andionea/steerturnillum/4_Engineering/1_Software/2_Development/1_Sources/4_EcuAbstraction/Btn/Design/SwDe_Btn.docx

Btn Software Design

SteerTurnIllum


Author: | | Nicolae-Bogdan Bacrău
Version: | | 1.0

# Index

# 1 Glossary

This section contains a glossary of all the important terms and acronyms used inside the document.

Term / Acronym | Description
AUTOSAR | AUTomotive Open System ARchitecture
VFB | Virtual Functional Bus
SWC | Software Component
RTE | Runtime Environment
BSW | Basic Software
OS | Operating System
S/R | Sender / Receiver
C/S | Client / Server
ECU | Electronic Control Unit
uC | Microcontroller
ADC | Analog Digital Converter
DIO | Digital Input / Output
PWM | Pulse Width Modulation

Table 1 - Glossary.

# 2 Introduction

## Purpose of the Document

The purpose of the document is to define the software design of the Btn SWC for the SteerTurnIllum embedded academy project.

## Overview

The Btn SWC implements the reading, debouncing and active values processing of all the button inputs, proving a simple button pressed or not pressed status.

# 3 Design Requirements

[SWDE_BTN_1] The Btn SWC shall adhere to the structure illustrated in the composite structure diagram from Figure 1.

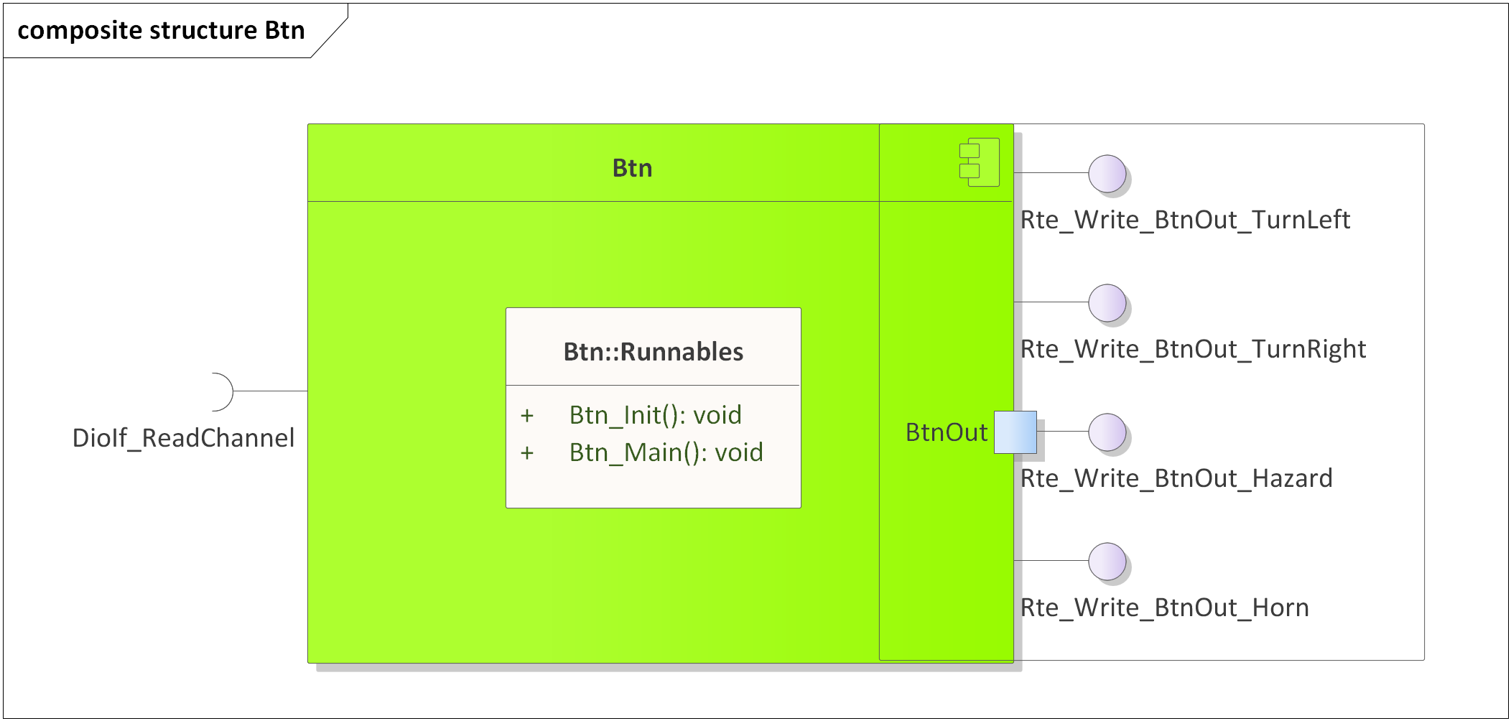
[picture p30: figure]

Figure 1 - Btn composite structure diagram.

[SWDE_BTN_2] The Btn SWC shall assure a debouncing mechanism according to Chapter 3.2 and [SYRE_GEN_11] from the System Requirements.
[SWDE_BTN_3] The Btn SWC shall adhere to the SWC file structure template from 4_Engineering\1_Software\2_Development\1_Sources\8_Templates\Swc\Code.
[SWDE_BTN_4] The Btn SWC shall contain the following configuration parameters:
- In Btn_Cfg.h:
  - BTN_MAIN_PERIODICITY_US: macro defining the periodicity of the main function in microseconds.
  - BTN_DEBOUNCE_WINDOW_US: macro defining the debounce window for all the buttons, in microseconds.
  - BTN_NUMBER_OF_INSTANCES: macro defining the number of button instances to be processed in the main function.
  - BTN_*_INSTANCE: zero based macros defining unique IDs of all the button instances, needed for the interaction between the core and RTE.
- In Btn_Cfg.c:
  - Btn_gkat_Config[BTN_NUMBER_OF_INSTANCES]: internal global constant array defining the active value (STD_HIGH or STD_LOW) and the DioIf channel for all the button channels.
[SWDE_BTN_5] The Btn SWC shall implement the void Btn_Init(void) runnable for initializing all the internal static and global variables.
[SWDE_BTN_6] The Btn SWC shall implement the void Btn_Main(void) runnable for implementing the processing of all the button instances as follows:
  - Reads the button DIO channels through DioIf_ReadChannel().
  - Calculates the current raw press state depending on the configured active press state in comparison with the actual read DIO level.
  - Applies the debounce algorithm on the current raw press state.
  - Writes the debounced buttons status to the RTE through Rte_Write_BtnOut_*(). RTE_BTN_INIT status shall be reported until a full (successful) debounce has been performed since the initialization.
[SWDE_BTN_7] The Btn SWC shall include DioIf.h and directly use the DioIf_ReadChannel() function for reading the button DioIf channels.

# 4 Information about this Document

## 1.1 Copyright

All rights, including translation rights, are reserved. Under no circumstances shall any fragment of this document be reproduced without written authorization from NTT DATA Romania S.A, including copying, photographing or replicating through other methods.

Copyright (c) NTT DATA Romania S.A.

## 1.2 Version Index

Version | Date | Author | Chapter | Modification description
1.0 | 10.07.2021 | Nicolae-Bogdan Bacrău | All | Created.

Table 2 - Version Index.

Copyright © NTT DATA Romania S.A. Page 6 of 7

Information Type: Working Standard Information Owner: Nicolae-Bogdan Bacrău Company: NTT DATA Romania
