andionea/steerturnillum/4_Engineering/1_Software/2_Development/1_Sources/5_Mcal/Dio/Design/SwDe_Dio.docx

Dio Software Design

SteerTurnIllum


Author: | | Nicolae-Bogdan Bacrău
Version: | | 1.0

# Index

# 1 Glossary

This section contains a glossary of all the important terms and acronyms used inside the document.

Term / Acronym | Description
AUTOSAR | AUTomotive Open System ARchitecture
VFB | Virtual Functional Bus
SWC | Software Component
RTE | Runtime Environment
BSW | Basic Software
OS | Operating System
S/R | Sender / Receiver
C/S | Client / Server
ECU | Electronic Control Unit
uC | Microcontroller
ADC | Analog Digital Converter
DIO | Digital Input / Output
PWM | Pulse Width Modulation

Table 1 - Glossary.

# 2 Introduction

## Purpose of the Document

The purpose of the document is to define the software design of the Dio driver for the SteerTurnIllum embedded academy project.

## Overview

While the AUTOSAR Dio module is complex and is usually configured via generators, in this project it is manually implemented and its features are limited to:

- Reading and writing channels.
- Reading and writing ports.

# 3 Design Requirements

[SWDE_DIO_1] The Dio driver shall be implemented according to AUTOSAR 4.3.1 specifications.
[SWDE_DIO_2] The Dio driver shall implement the following interfaces and all their required data types for reading and writing DIO channels and ports:
- Dio_ReadChannel();
- Dio_WriteChannel();
- Dio_FlipChannel();
- Dio_ReadPort();
- Dio_WritePort();
[SWDE_DIO_3] The Dio driver shall consist of the following files:
- Dio.c: Implements all the required interfaces in a generic way.
- Dio.h: Exports all the required interfaces, data types and the link-time configuration.
- Dio_Lcfg.c: Defines the list of registers and masks to be used for reading and writing DIO channels and ports.
- Dio_Cfg.h: Defines and exports the following:
  - DIO_API_CHANNELS macro: defining if the DIO channels APIs are activated or not (STD_ON or STD_OFF).
  - DIO_API_PORTS macro: defining if the DIO ports APIs are activated or not (STD_ON or STD_OFF).
  - DIO_NUMBER_OF_PORTS macro: number of configured DIO ports.
  - DIO_<Port_ID> macros: zero based IDs of all the DIO ports.
  - DIO_NUMBER_OF_CHANNELS macro: number of configured DIO channels.
  - DIO_<Port_ID>_<Port_Pin_ID> macros: zero based IDs of all the DIO channels.

# 4 Information about this Document

## 1.1 Copyright

All rights, including translation rights, are reserved. Under no circumstances shall any fragment of this document be reproduced without written authorization from NTT DATA Romania S.A, including copying, photographing or replicating through other methods.

Copyright (c) NTT DATA Romania S.A.

## 1.2 Version Index

Version | Date | Author | Chapter | Modification description
1.0 | 10.07.2021 | Nicolae-Bogdan Bacrău | All | Created.

Table 2 - Version Index.

Copyright © NTT DATA Romania S.A. Page 6 of 7

Information Type: Working Standard Information Owner: Nicolae-Bogdan Bacrău Company: NTT DATA Romania
