andionea/steerturnillum/4_Engineering/1_Software/2_Development/1_Sources/5_Mcal/Pwm/Design/SwDe_Pwm.docx

Pwm Software Design

SteerTurnIllum


Author: | | Nicolae-Bogdan Bacrău
Version: | | 1.0

# Index

# 1 Glossary

This section contains a glossary of all the important terms and acronyms used inside the document.

Term / Acronym | Description
AUTOSAR | AUTomotive Open System ARchitecture
VFB | Virtual Functional Bus
SWC | Software Component
RTE | Runtime Environment
BSW | Basic Software
OS | Operating System
S/R | Sender / Receiver
C/S | Client / Server
ECU | Electronic Control Unit
uC | Microcontroller
ADC | Analog Digital Converter
DIO | Digital Input / Output
PWM | Pulse Width Modulation

Table 1 - Glossary.

# 2 Introduction

## Purpose of the Document

The purpose of the document is to define the software design of the Pwm driver for the SteerTurnIllum embedded academy project.

## Overview

While the AUTOSAR Pwm module is complex and is usually configured via generators, in this project it is manually implemented and its features are limited to:

- Configuring PWM channels.
- Writing PWM duty cycles.

# 3 Design Requirements

[SWDE_PWM_1] The Pwm driver shall be implemented according to AUTOSAR 4.3.1 specifications.
[SWDE_PWM_2] The Pwm driver shall implement the following interfaces and all their required data types for configuring PWM channels (timer configurations) and writing PWM duty cycles:
- Pwm_Init();
- Pwm_SetDutyCycle();
[SWDE_PWM_3] The Pwm driver shall include Init.h and directly use the Init_gv_Full*Bits() and / or Init_gv_Masked*Bits() functions for loading registers.
[SWDE_PWM_4] The Pwm driver shall consist of the following files:
- Pwm.c: Implements all the required interfaces in a generic way.
- Pwm.h: Exports all the required interfaces, data types and the post-build configuration.
- Pwm_PBcfg.c: Defines the list of registers and values to be written for setting the timers in PWM mode, setting the periods of the PWM channels and the PWM initial duty cycles.
- Pwm_Cfg.h: Defines and exports the following:
  - PWM_API_SET_DUTY_CYCLE macro: defining if the PWM API for setting duty cycles is activated or not (STD_ON or STD_OFF).
  - PWM_NUMBER_OF_CHANNELS macro: number of configured PWM channels.
  - PWM_<Port_ID>_<Port_Pin_ID> macros: zero based IDs of all the PWM channels.

# 4 Information about this Document

## 1.1 Copyright

All rights, including translation rights, are reserved. Under no circumstances shall any fragment of this document be reproduced without written authorization from NTT DATA Romania S.A, including copying, photographing or replicating through other methods.

Copyright (c) NTT DATA Romania S.A.

## 1.2 Version Index

Version | Date | Author | Chapter | Modification description
1.0 | 10.07.2021 | Nicolae-Bogdan Bacrău | All | Created.

Table 2 - Version Index.

Copyright © NTT DATA Romania S.A. Page 6 of 7

Information Type: Working Standard Information Owner: Nicolae-Bogdan Bacrău Company: NTT DATA Romania
