andionea/steerturnillum/4_Engineering/1_Software/2_Development/1_Sources/4_EcuAbstraction/Buzz/Design/SwDe_Buzz.docx

Buzz Software Design

SteerTurnIllum


Author: | | Nicolae-Bogdan Bacrău
Version: | | 1.0

# Index

# 1 Glossary

This section contains a glossary of all the important terms and acronyms used inside the document.

Term / Acronym | Description
AUTOSAR | AUTomotive Open System ARchitecture
VFB | Virtual Functional Bus
SWC | Software Component
RTE | Runtime Environment
BSW | Basic Software
OS | Operating System
S/R | Sender / Receiver
C/S | Client / Server
ECU | Electronic Control Unit
uC | Microcontroller
ADC | Analog Digital Converter
DIO | Digital Input / Output
PWM | Pulse Width Modulation

Table 1 - Glossary.

# 2 Introduction

## Purpose of the Document

The purpose of the document is to define the software design of the Buzz SWC for the SteerTurnIllum embedded academy project.

## Overview

The Buzz SWC implements a simple mute or buzzing control of buzzers.

# 3 Design Requirements

[SWDE_BUZZ_1] The Buzz SWC shall adhere to the structure illustrated in the composite structure diagram from Figure 1.

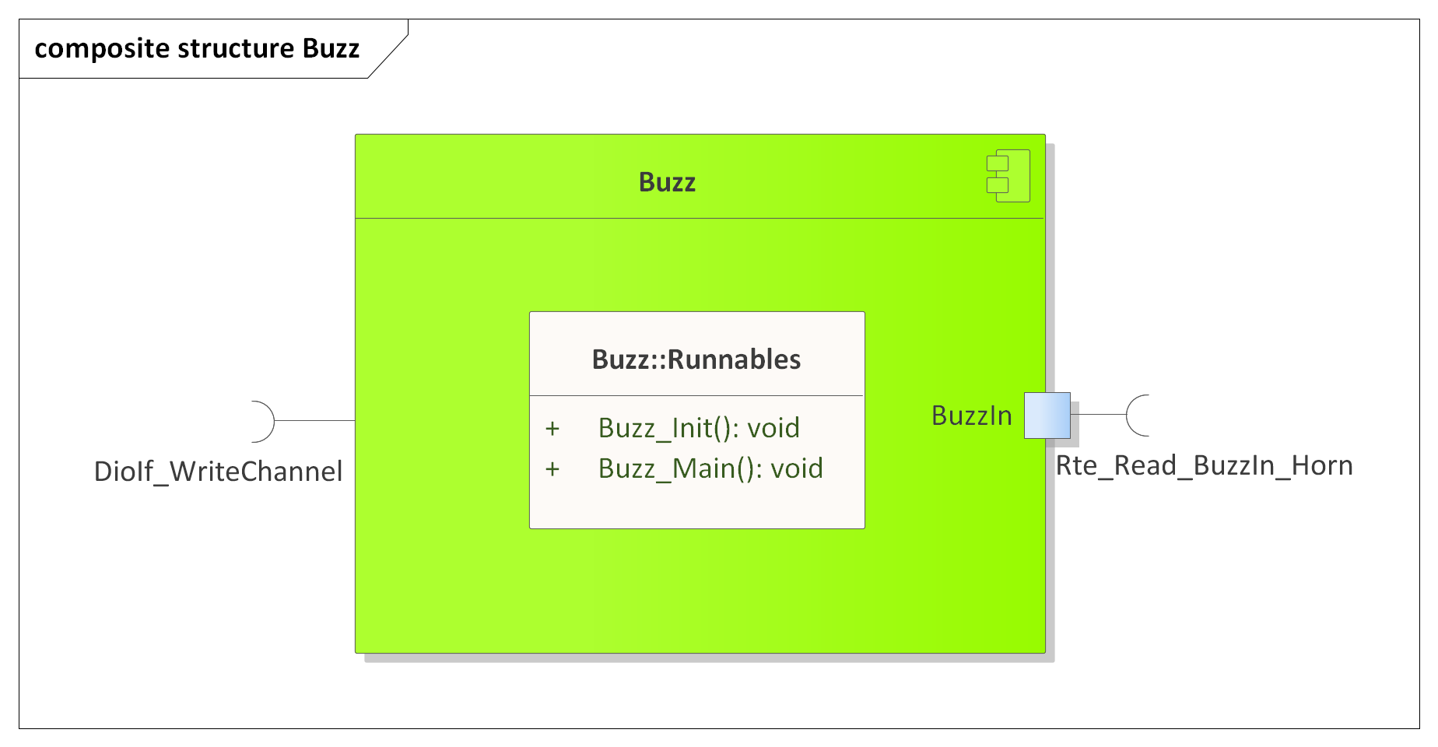
[picture p34: figure]

Figure 1 - Buzz composite structure diagram.

[SWDE_BUZZ_2] The Buzz SWC shall adhere to the SWC file structure template from 4_Engineering\1_Software\2_Development\1_Sources\8_Templates\Swc\Code.
[SWDE_BUZZ_3] The Buzz SWC shall contain the following configuration parameters:
- In Buzz_Cfg.h:
  - BUZZ_NUMBER_OF_INSTANCES: macro defining the number of buzzer instances to be processed in the main function.
  - BUZZ_*_INSTANCE: zero based macros defining unique IDs of all the buzzer instances, needed for the interaction between the core and RTE.
- In Buzz_Cfg.c:
  - Buzz_gkat_Config[BUZZ_NUMBER_OF_INSTANCES]: internal global constant array defining the VCC and IO DioIf channels for all buzzer instances.
[SWDE_BUZZ_4] The Buzz SWC shall implement the void Buzz_Init(void) runnable for initializing all the internal static and global variables and setting the buzzer in the mute state through DioIf_WriteChannel().
[SWDE_BUZZ_5] The Buzz SWC shall implement the void Buzz_Main(void) runnable for implementing the processing of all the buzzer instances as follows:
  - Reads the buzzer input control data through Rte_Read_BuzzIn_*().
  - Sets the buzzer state according to the read input control data: mute if RTE_BUZZ_OFF, buzzing if RTE_BUZZ_ON, through DioIf_WriteChannel(). Any other input control value shall be ignored.
[SWDE_BUZZ_6] The Buzz SWC shall include DioIf.h and directly use the DioIf_WriteChannel() function for writing the buzzer DioIf channels.

# 4 Information about this Document

## 1.1 Copyright

All rights, including translation rights, are reserved. Under no circumstances shall any fragment of this document be reproduced without written authorization from NTT DATA Romania S.A, including copying, photographing or replicating through other methods.

Copyright (c) NTT DATA Romania S.A.

## 1.2 Version Index

Version | Date | Author | Chapter | Modification description
1.0 | 10.07.2021 | Nicolae-Bogdan Bacrău | All | Created.

Table 2 - Version Index.

Copyright © NTT DATA Romania S.A. Page 6 of 7

Information Type: Working Standard Information Owner: Nicolae-Bogdan Bacrău Company: NTT DATA Romania
