andionea/steerturnillum/4_Engineering/1_Software/2_Development/1_Sources/7_Libraries/Efx/Design/SwDe_Efx.docx

Efx Software Design

SteerTurnIllum


Author: | | Nicolae-Bogdan Bacrău
Version: | | 1.0

# Index

# 1 Glossary

This section contains a glossary of all the important terms and acronyms used inside the document.

Term / Acronym | Description
AUTOSAR | AUTomotive Open System ARchitecture
VFB | Virtual Functional Bus
SWC | Software Component
RTE | Runtime Environment
BSW | Basic Software
OS | Operating System
S/R | Sender / Receiver
C/S | Client / Server
ECU | Electronic Control Unit
uC | Microcontroller
ADC | Analog Digital Converter
DIO | Digital Input / Output
PWM | Pulse Width Modulation

Table 1 - Glossary.

# 2 Introduction

## Purpose of the Document

The purpose of the document is to define the software design of the Efx library for the SteerTurnIllum embedded academy project.

## Overview

While the AUTOSAR Efx library contains more methods, in this project it implements a single interface for performing moving averages on uint16 inputs and outputs.

# 3 Design Requirements

[SWDE_EFX_1] The Efx library shall be implemented according to AUTOSAR 4.3.1 specifications.
[SWDE_EFX_2] The Efx library shall implement the following interfaces and all their required data types for performing moving averages on uint16 inputs and outputs (see “8.5.8 Moving Average” on page 68):
- Efx_MovingAverage_u16_u16();
[SWDE_EFX_3] The Efx library shall consist of the following files:
- Efx.c: Implements all the required interfaces in a generic way.
- Efx.h: Exports all the required interfaces and data types.

# 4 Information about this Document

## 1.1 Copyright

All rights, including translation rights, are reserved. Under no circumstances shall any fragment of this document be reproduced without written authorization from NTT DATA Romania S.A, including copying, photographing or replicating through other methods.

Copyright (c) NTT DATA Romania S.A.

## 1.2 Version Index

Version | Date | Author | Chapter | Modification description
1.0 | 10.07.2021 | Nicolae-Bogdan Bacrău | All | Created.

Table 2 - Version Index.

Copyright © NTT DATA Romania S.A. Page 6 of 7

Information Type: Working Standard Information Owner: Nicolae-Bogdan Bacrău Company: NTT DATA Romania
