andionea/steerturnillum/4_Engineering/1_Software/2_Development/1_Sources/2_Rte/Code/Specific/Rte_SwPwm.h

/*-------------------------------------------------------------------------------------------------------------------*/
/**
 *    \file       Rte_SwPwm.h
 *    \author     RTE Generator
 *    \brief      Generated file - shall not be manually edited. 
 *                Implements all the RTE read and write operations that are performed by the SwPwm software
 *                component.
 */
/*-------------------------------------------------------------------------------------------------------------------*/

#ifndef RTE_SWPWM_H
#define RTE_SWPWM_H

/*-------------------------------------------------------------------------------------------------------------------*/
/*                                                     Inclusions                                                    */
/*-------------------------------------------------------------------------------------------------------------------*/

#include "Rte.h"

/*-------------------------------------------------------------------------------------------------------------------*/
/*                                            Definition Of Global Macros                                            */
/*-------------------------------------------------------------------------------------------------------------------*/

#define Rte_IsUpdated_SwPwmIn_Horn() (Rte_SwPwmControl_SwPwmIn_Horn_UpdateFlag)
#define Rte_Read_SwPwmIn_Horn(x) \
   do \
   { \
      (*x) = Rte_SwPwmControl_Horn_Buf; \
      Rte_SwPwmControl_SwPwmIn_Horn_UpdateFlag = FALSE; \
   } while(0)
#define Rte_IsUpdated_SwPwmIn_Turn() (Rte_SwPwmControl_SwPwmIn_Turn_UpdateFlag)
#define Rte_Read_SwPwmIn_Turn(x) \
   do \
   { \
      (*x) = Rte_SwPwmControl_Turn_Buf; \
      Rte_SwPwmControl_SwPwmIn_Turn_UpdateFlag = FALSE; \
   } while(0)

#define Rte_Write_SwPwmOut_Horn(x) (Rte_SwPwmStatus_Horn_Buf = (*x))
#define Rte_Write_SwPwmOut_Turn(x) (Rte_SwPwmStatus_Turn_Buf = (*x))

/*-------------------------------------------------------------------------------------------------------------------*/
/*                                          Definition Of Global Data Types                                          */
/*-------------------------------------------------------------------------------------------------------------------*/

/*-------------------------------------------------------------------------------------------------------------------*/
/*                                             Export Of Global Variables                                            */
/*-------------------------------------------------------------------------------------------------------------------*/

/*-------------------------------------------------------------------------------------------------------------------*/
/*                                             Export Of Global Constants                                            */
/*-------------------------------------------------------------------------------------------------------------------*/

/*-------------------------------------------------------------------------------------------------------------------*/
/*                                             Export Of Global Functions                                            */
/*-------------------------------------------------------------------------------------------------------------------*/

/*-------------------------------------------------------------------------------------------------------------------*/
#endif /* RTE_SWPWM_H */
