andionea/steerturnillum/4_Engineering/1_Software/2_Development/1_Sources/2_Rte/Code/Specific/Rte_Fade.h

/*-------------------------------------------------------------------------------------------------------------------*/
/**
 *    \file       Rte_Fade.h
 *    \author     RTE Generator
 *    \brief      Generated file - shall not be manually edited. 
 *                Implements all the RTE read and write operations that are performed by the Fade software
 *                component.
 */
/*-------------------------------------------------------------------------------------------------------------------*/

#ifndef RTE_FADE_H
#define RTE_FADE_H

/*-------------------------------------------------------------------------------------------------------------------*/
/*                                                     Inclusions                                                    */
/*-------------------------------------------------------------------------------------------------------------------*/

#include "Rte.h"

/*-------------------------------------------------------------------------------------------------------------------*/
/*                                            Definition Of Global Macros                                            */
/*-------------------------------------------------------------------------------------------------------------------*/

#define Rte_IsUpdated_FadeIn_IllumDay() (Rte_FadeControl_FadeIn_IllumDay_UpdateFlag)
#define Rte_Read_FadeIn_IllumDay(x) \
   do \
   { \
      (*x) = Rte_FadeControl_IllumDay_Buf; \
      Rte_FadeControl_FadeIn_IllumDay_UpdateFlag = FALSE; \
   } while(0)
#define Rte_IsUpdated_FadeIn_IllumNight() (Rte_FadeControl_FadeIn_IllumNight_UpdateFlag)
#define Rte_Read_FadeIn_IllumNight(x) \
   do \
   { \
      (*x) = Rte_FadeControl_IllumNight_Buf; \
      Rte_FadeControl_FadeIn_IllumNight_UpdateFlag = FALSE; \
   } while(0)

#define Rte_Write_FadeOut_IllumDay(x) (Rte_FadeStatus_IllumDay_Buf = (*x))
#define Rte_Write_FadeOut_IllumNight(x) (Rte_FadeStatus_IllumNight_Buf = (*x))

/*-------------------------------------------------------------------------------------------------------------------*/
/*                                          Definition Of Global Data Types                                          */
/*-------------------------------------------------------------------------------------------------------------------*/

/*-------------------------------------------------------------------------------------------------------------------*/
/*                                             Export Of Global Variables                                            */
/*-------------------------------------------------------------------------------------------------------------------*/

/*-------------------------------------------------------------------------------------------------------------------*/
/*                                             Export Of Global Constants                                            */
/*-------------------------------------------------------------------------------------------------------------------*/

/*-------------------------------------------------------------------------------------------------------------------*/
/*                                             Export Of Global Functions                                            */
/*-------------------------------------------------------------------------------------------------------------------*/

/*-------------------------------------------------------------------------------------------------------------------*/
#endif /* RTE_FADE_H */
