andionea/steerturnillum/4_Engineering/1_Software/2_Development/1_Sources/2_Rte/Code/Specific/Rte_Led.h

/*-------------------------------------------------------------------------------------------------------------------*/
/**
 *    \file       Rte_Led.h
 *    \author     RTE Generator
 *    \brief      Generated file - shall not be manually edited. 
 *                Implements all the RTE read and write operations that are performed by the Led software
 *                component.
 */
/*-------------------------------------------------------------------------------------------------------------------*/

#ifndef RTE_LED_H
#define RTE_LED_H

/*-------------------------------------------------------------------------------------------------------------------*/
/*                                                     Inclusions                                                    */
/*-------------------------------------------------------------------------------------------------------------------*/

#include "Rte.h"

/*-------------------------------------------------------------------------------------------------------------------*/
/*                                            Definition Of Global Macros                                            */
/*-------------------------------------------------------------------------------------------------------------------*/

#define Rte_Read_LedIn_TurnFrontLeft(x) ((*x) = Rte_LedControl_TurnFrontLeft_Buf)
#define Rte_Read_LedIn_TurnFrontRight(x) ((*x) = Rte_LedControl_TurnFrontRight_Buf)
#define Rte_Read_LedIn_TurnBackLeft(x) ((*x) = Rte_LedControl_TurnBackLeft_Buf)
#define Rte_Read_LedIn_TurnBackRight(x) ((*x) = Rte_LedControl_TurnBackRight_Buf)
#define Rte_Read_LedIn_IllumDay(x) ((*x) = Rte_LedControl_IllumDay_Buf)
#define Rte_Read_LedIn_IllumNight(x) ((*x) = Rte_LedControl_IllumNight_Buf)

/*-------------------------------------------------------------------------------------------------------------------*/
/*                                          Definition Of Global Data Types                                          */
/*-------------------------------------------------------------------------------------------------------------------*/

/*-------------------------------------------------------------------------------------------------------------------*/
/*                                             Export Of Global Variables                                            */
/*-------------------------------------------------------------------------------------------------------------------*/

/*-------------------------------------------------------------------------------------------------------------------*/
/*                                             Export Of Global Constants                                            */
/*-------------------------------------------------------------------------------------------------------------------*/

/*-------------------------------------------------------------------------------------------------------------------*/
/*                                             Export Of Global Functions                                            */
/*-------------------------------------------------------------------------------------------------------------------*/

/*-------------------------------------------------------------------------------------------------------------------*/
#endif /* RTE_LED_H */
