andionea/steerturnillum/4_Engineering/1_Software/2_Development/1_Sources/5_Mcal/Adc/Code/Specific/Adc_Cfg.h

/*-------------------------------------------------------------------------------------------------------------------*/
/**
 *    \file       Adc_Cfg.h
 *    \author     Andrei-Cristian Onea
 *    \brief      
 */
/*-------------------------------------------------------------------------------------------------------------------*/

#ifndef ADC_CFG_H
#define ADC_CFG_H

/*-------------------------------------------------------------------------------------------------------------------*/
/*                                                     Inclusions                                                    */
/*-------------------------------------------------------------------------------------------------------------------*/

/*-------------------------------------------------------------------------------------------------------------------*/
/*                                            Definition Of Global Macros                                            */
/*-------------------------------------------------------------------------------------------------------------------*/

/** \brief     Defines the total number of configured ADC Channels. */
#define ADC_NUMBER_OF_GROUPS            (2U)   

/** \brief     PA1 */
#define ADC_A_1     (0U)

/** \brief     PC2 */
#define ADC_C_2     (1U)

/*-------------------------------------------------------------------------------------------------------------------*/
/*                                          Definition Of Global Data Types                                          */
/*-------------------------------------------------------------------------------------------------------------------*/

/*-------------------------------------------------------------------------------------------------------------------*/
/*                                             Export Of Global Variables                                            */
/*-------------------------------------------------------------------------------------------------------------------*/

/*-------------------------------------------------------------------------------------------------------------------*/
/*                                             Export Of Global Constants                                            */
/*-------------------------------------------------------------------------------------------------------------------*/

/*-------------------------------------------------------------------------------------------------------------------*/
/*                                             Export Of Global Functions                                            */
/*-------------------------------------------------------------------------------------------------------------------*/

/*-------------------------------------------------------------------------------------------------------------------*/
#endif /* ADC_CFG_H */
